andresbott/project-athena/bottomSSD/2.5_SSD_enclosure.jpg

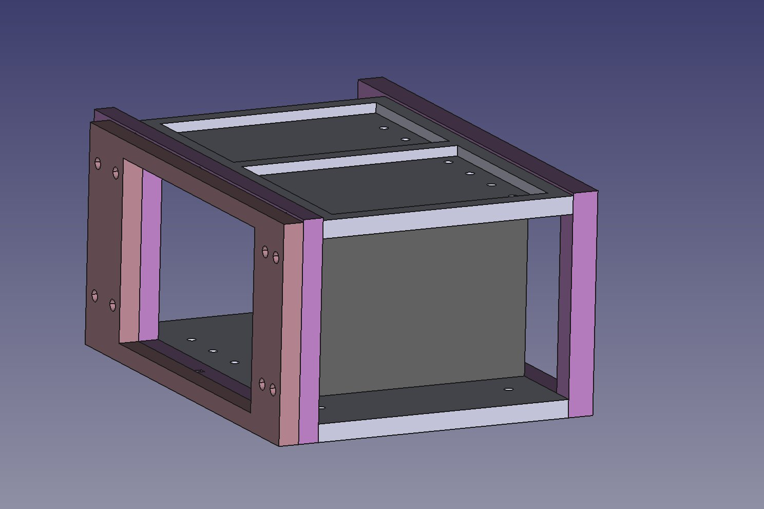
bottomSSD/2.5_SSD_enclosure.jpg
