andresbott/project-athena/frontCover/fronCover.jpg

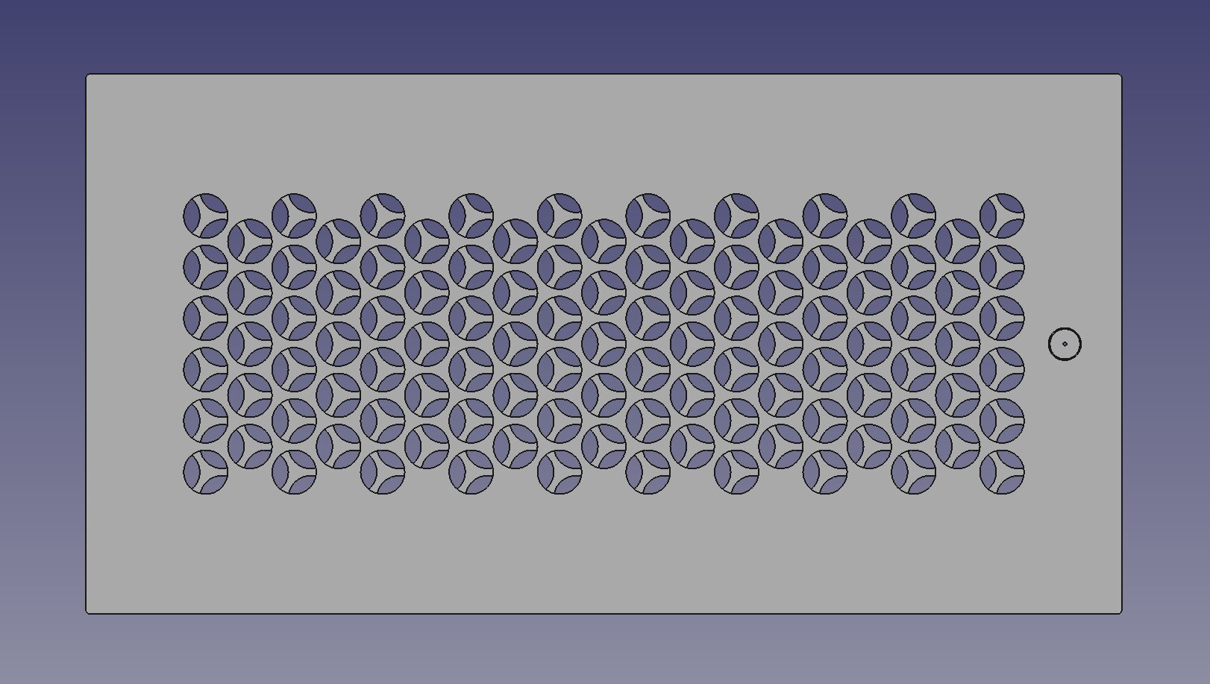
frontCover/fronCover.jpg
