andresbott/project-athena/bottomSSD/files/SSDEnclosureBottom-Back.obj

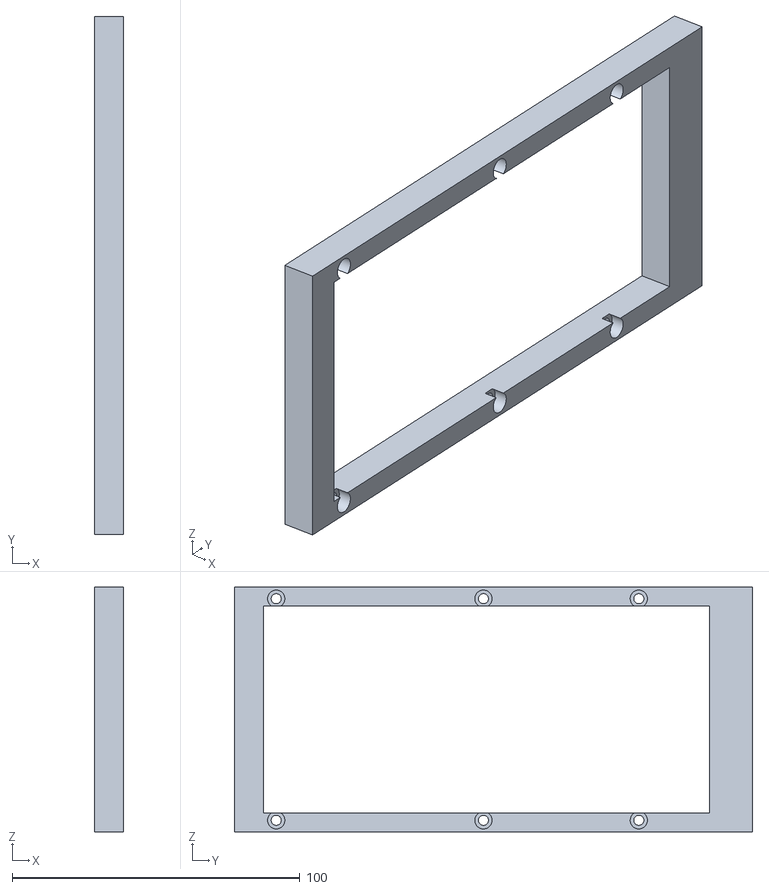
[picture p25: CAD file, 2025-08-28]
bottomSSD/files/SSDEnclosureBottom-Back.obj
10.0 x 180.0 x 85.0
