andresbott/project-athena/frontCover/files/frontCover-FrontPannel_bottom.amf

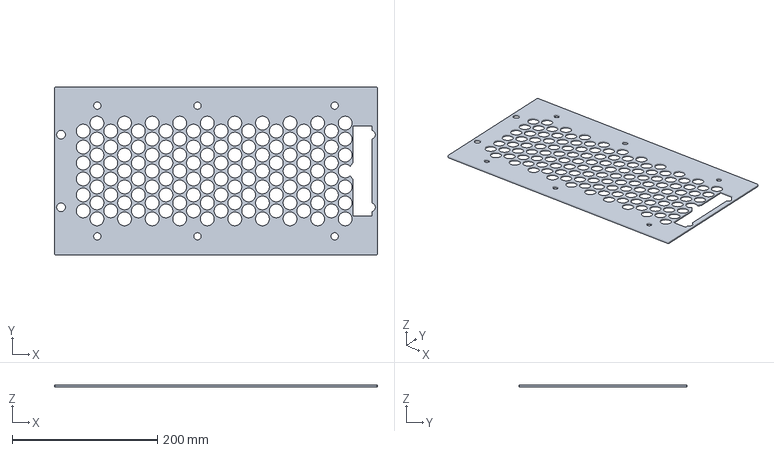
[picture p26: CAD file, 2025-08-28]
frontCover/files/frontCover-FrontPannel_bottom.amf
445.0 x 232.0 x 3.00 mm
