andresbott/project-athena/HDDEnclosure/files/HDDEnclosure-FrontV2.obj

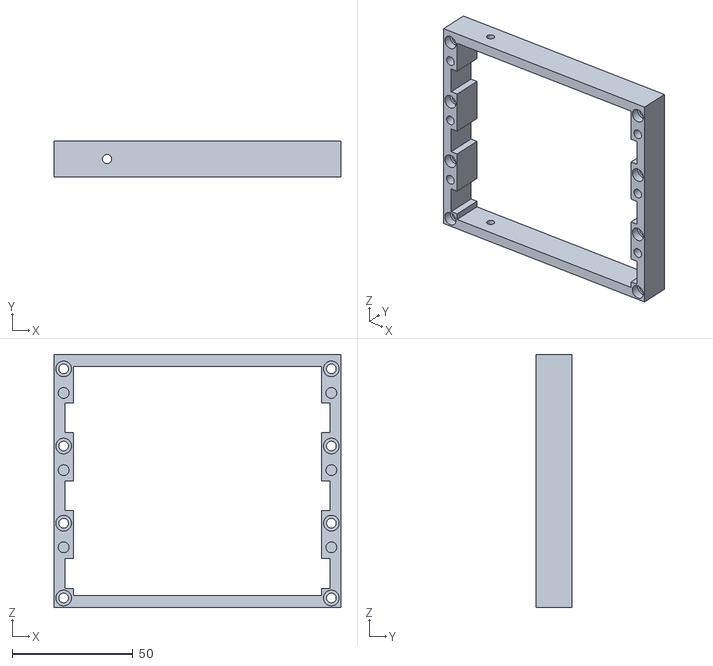
[picture p27: CAD file, 2025-08-28]
HDDEnclosure/files/HDDEnclosure-FrontV2.obj
119.0 x 15.0 x 105.0
