andresbott/project-athena/bottomSSD/files/SSDEnclosureBottom-frontBracket.obj

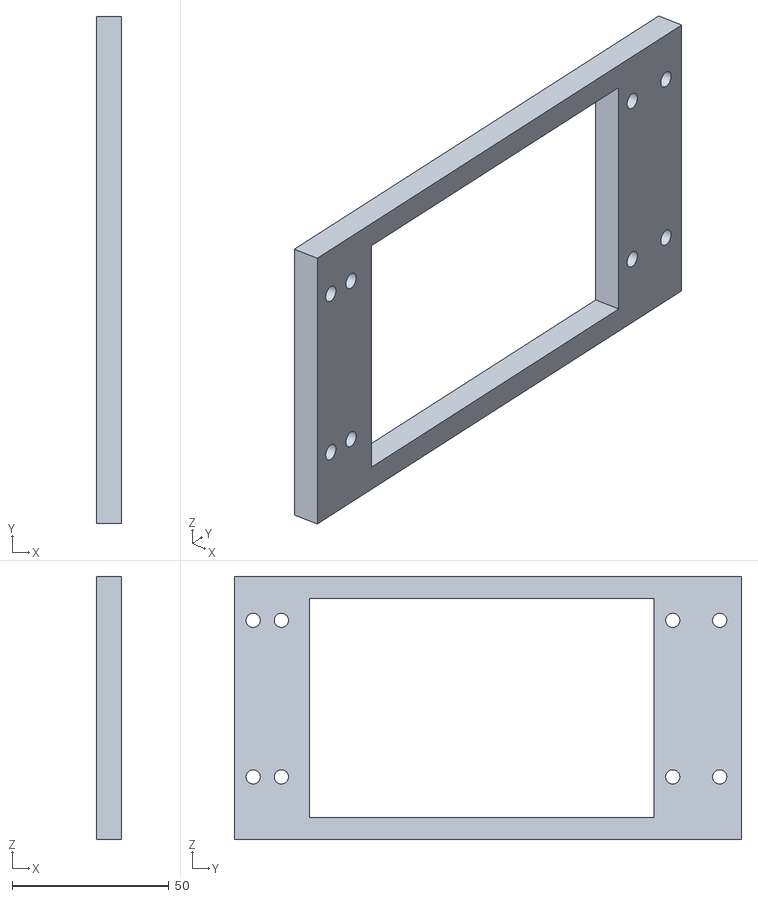
[picture p28: CAD file, 2025-08-28]
bottomSSD/files/SSDEnclosureBottom-frontBracket.obj
8.00 x 162.0 x 84.0
