andresbott/project-athena/frontCover/files/frontCover-Button.obj

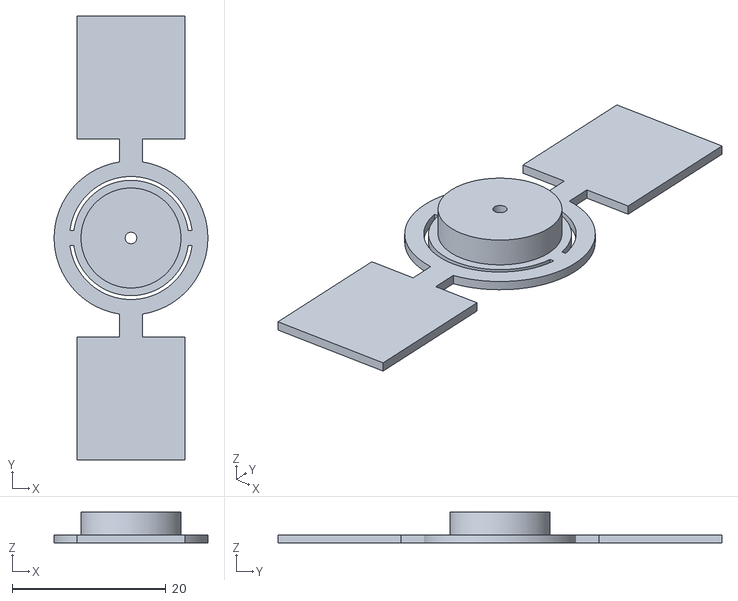
[picture p29: CAD file, 2025-08-28]
frontCover/files/frontCover-Button.obj
20.0 x 57.8 x 4.00
