andresbott/project-athena/frontCover/files/frontCover-frontPlateHolder.obj

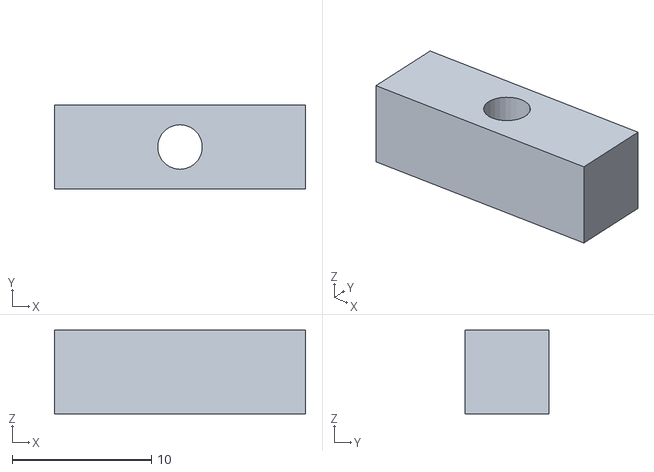
[picture p30: CAD file, 2025-08-28]
frontCover/files/frontCover-frontPlateHolder.obj
18.0 x 6.00 x 6.00
