andresbott/project-athena/HDDEnclosure/files/HDDEnclosure-BackV2.obj

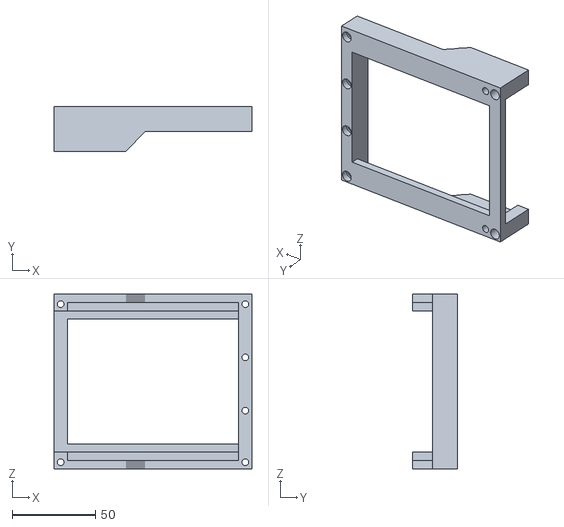
[picture p31: CAD file, 2025-08-28]
HDDEnclosure/files/HDDEnclosure-BackV2.obj
119.0 x 27.0 x 105.0
